the-Fish2/techrise/IMG_20221002_223637890.jpg

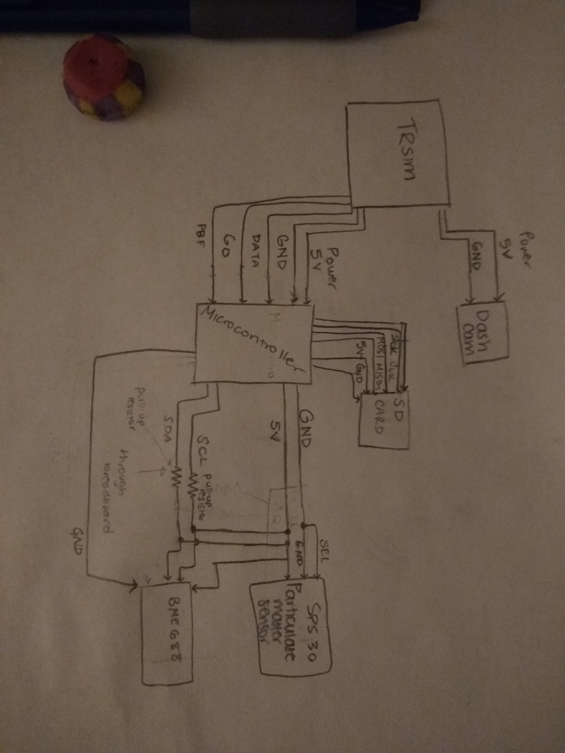
IMG_20221002_223637890.jpg
